collabbots/collabbots-v1.0/hardware/pcbs/simulations/pushbutton-debounce/pushbutton-debounce-circuitry.asc

C1: cap; 5µ
R1: res; 100k
R2: res; 10k
V1: voltage; PWL(0 0 0.2 0 0.2009 2 0.2015 3.3 0.2020 2 0.2025 0 0.3 0 0.3001 3.3 0.4 3.3 0.5 3.3 0.6 3.3 0.7 3.3 1 3.3)
Named nets: 0
.tran 0 0.5 0.19 startup
