collabbots/collabbots-v1.0/hardware/pcbs/simulations/relay-driver/G5LE-relay-coil-driver-circuitry.asc

D1: diode; 1N4148
L1: ind; 100m; Ipk=79.4m Rser=63
Q1: npn; BC547C
Q2: npn; BC547C
R1: res; 100
R2: res; 1k
V1: voltage; PULSE(0 3.3 0 0 0 0.5 1 5)
V2: voltage; 5
Named nets: 0
.tran 0 5 0 startup
